TobiasVanDyk/Bass-Treble-and-Volume-USB-Controller-with-Keyboard-LEDs/images/Photo2.jpg

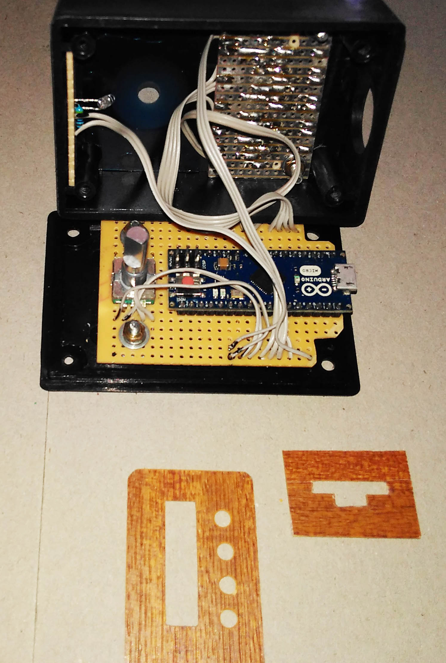
images/Photo2.jpg
