TobiasVanDyk/Bass-Treble-and-Volume-USB-Controller-with-Keyboard-LEDs/images/Photo3.jpg

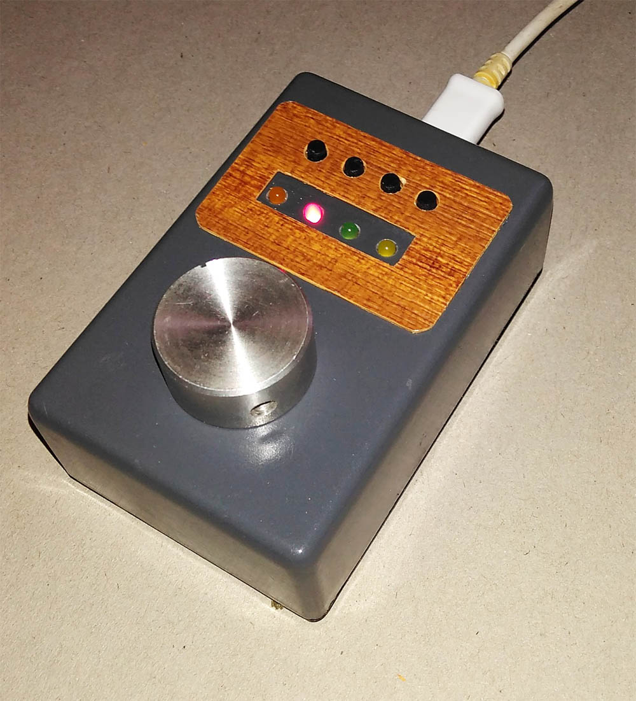
images/Photo3.jpg
